sixhat/Pintografo/briefing/assets/pintograph-02.jpeg

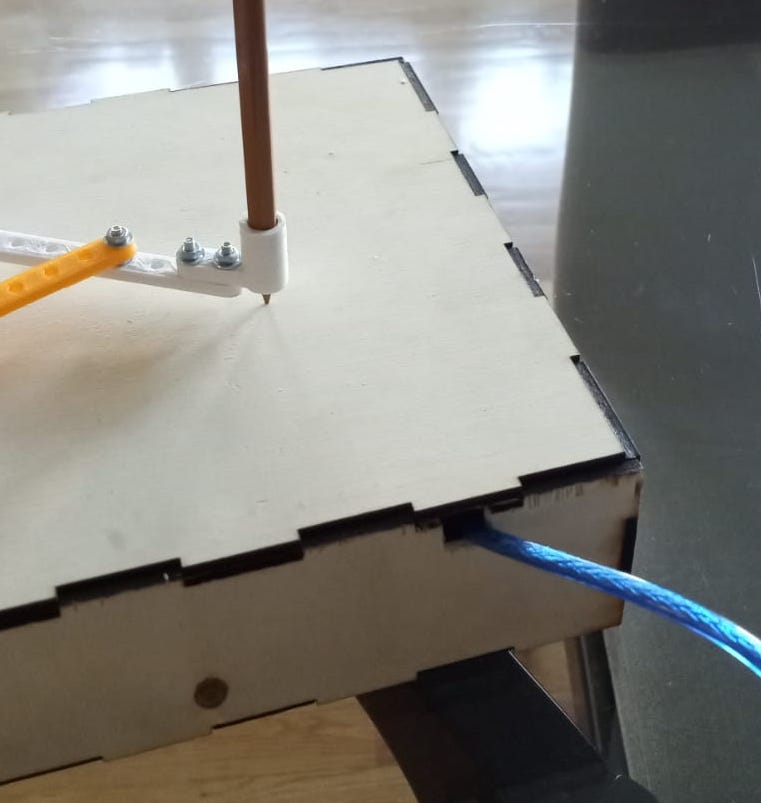
briefing/assets/pintograph-02.jpeg
