sixhat/Pintografo/briefing/assets/ULN2003.jpg

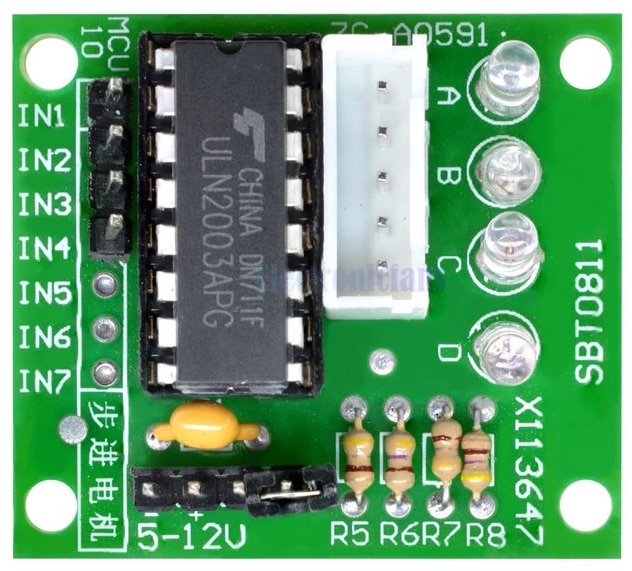
briefing/assets/ULN2003.jpg
