sixhat/Pintografo/media/arms-on-off-button.jpeg

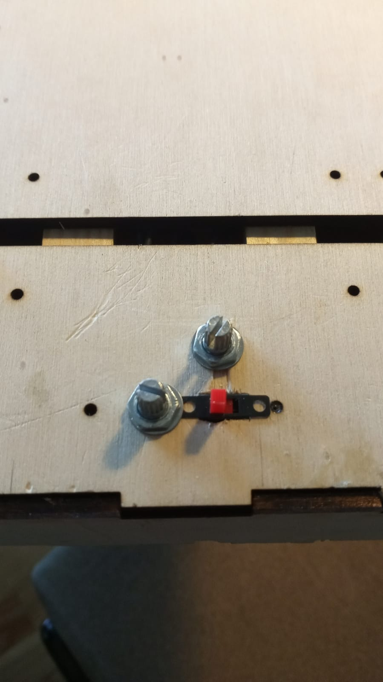
media/arms-on-off-button.jpeg
