sixhat/Pintografo/media/byj-48-steppers.jpeg

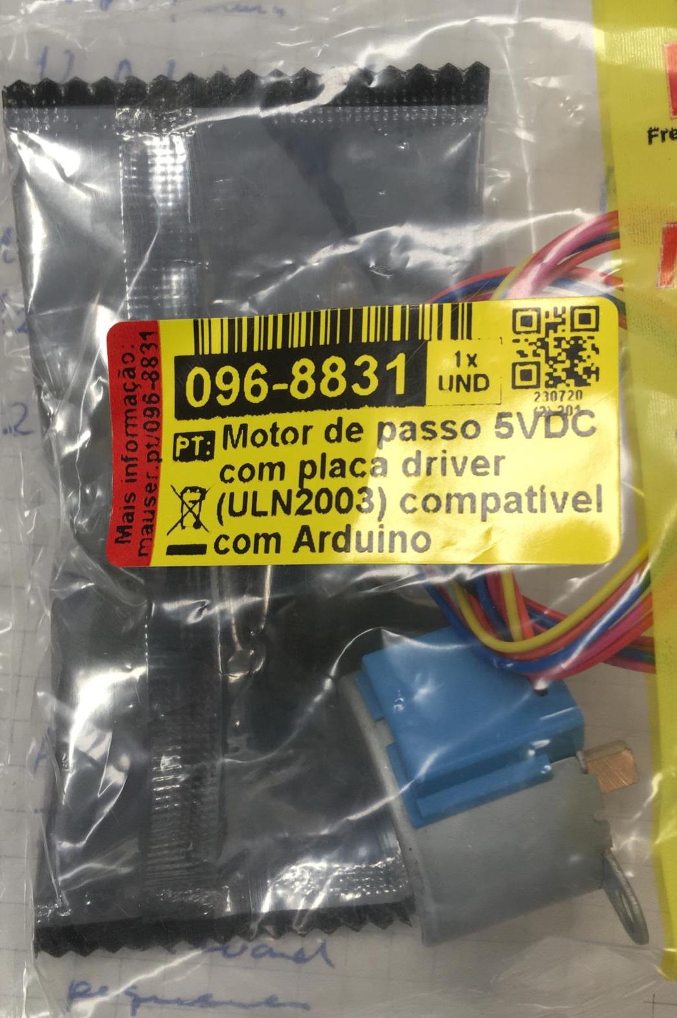
media/byj-48-steppers.jpeg
