sixhat/Pintografo/media/drawing-machine-internals-02.jpeg

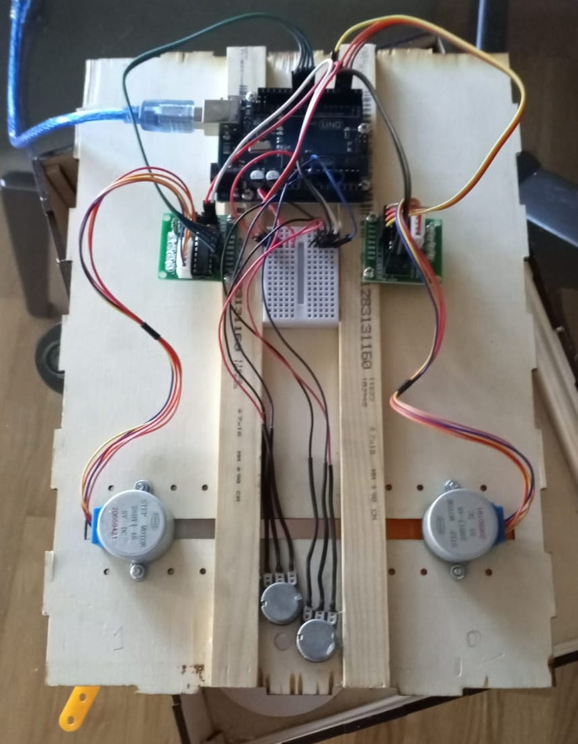
media/drawing-machine-internals-02.jpeg
