sixhat/Pintografo/media/drawing-machine-internals.jpeg

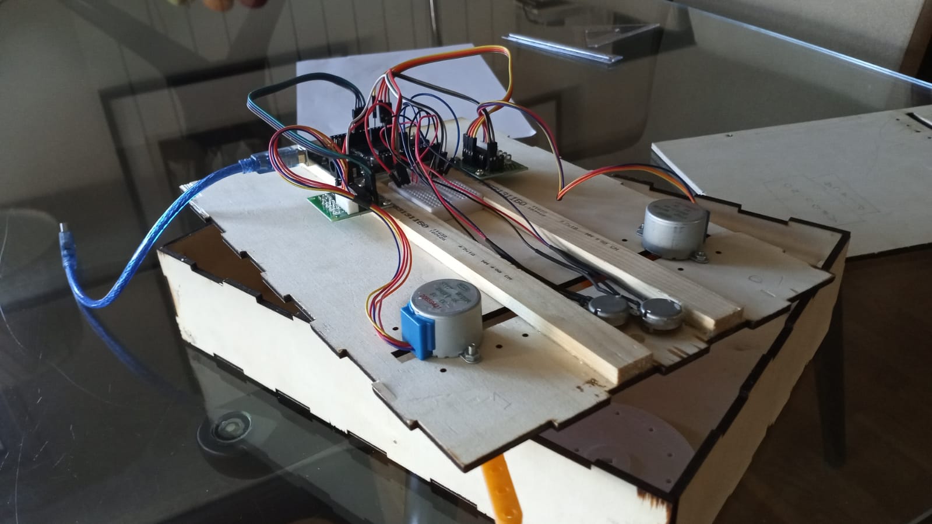
media/drawing-machine-internals.jpeg
