sixhat/Pintografo/media/prototype-working.jpeg

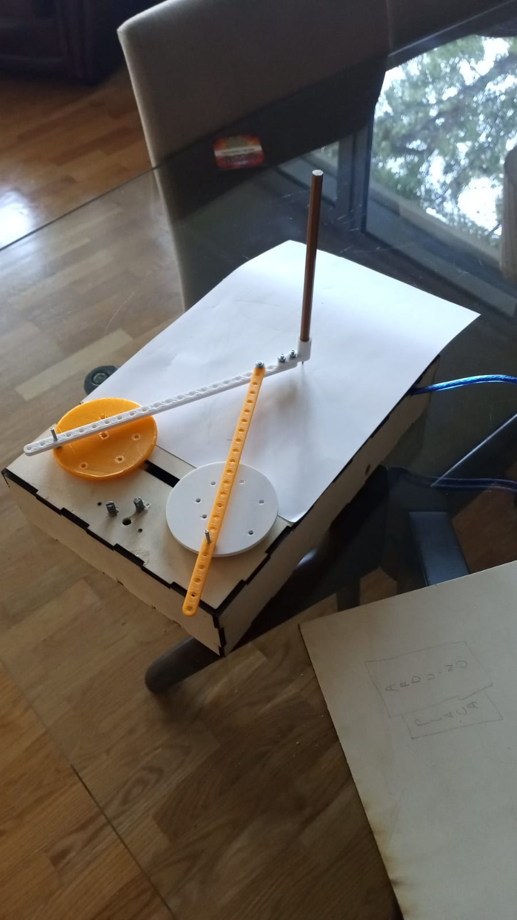
media/prototype-working.jpeg
