sixhat/Pintografo/3Dprinting/stl/pen_holder.stl

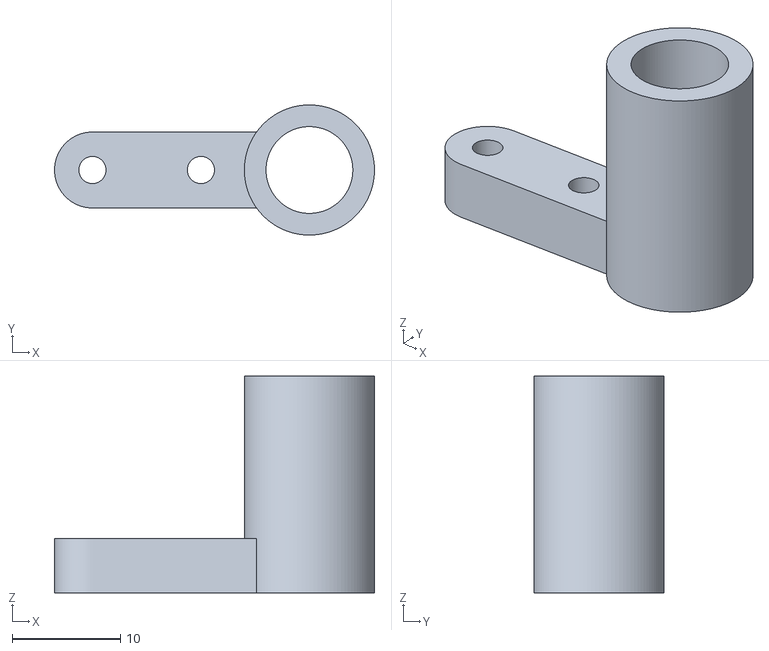
[picture p27: CAD file, 2022-09-26]
3Dprinting/stl/pen_holder.stl
29.5 x 12.0 x 20.0
