sixhat/Pintografo/3Dprinting/stl/spindles_v4.stl

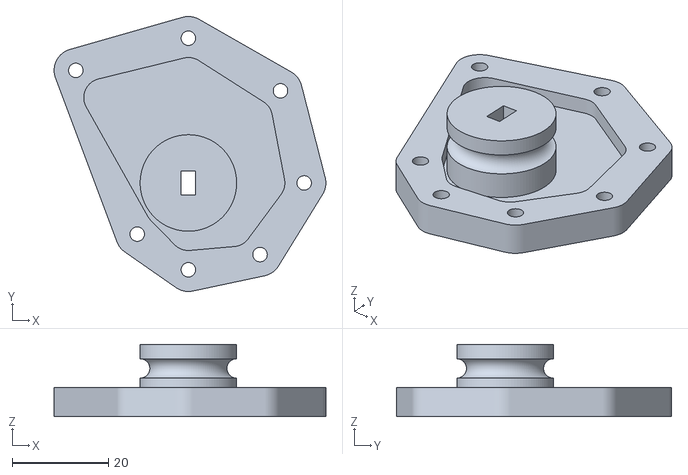
[picture p28: CAD file, 2022-10-15, an earlier design]
3Dprinting/stl/spindles_v4.stl
56.3 x 57.0 x 15.0
