sixhat/Pintografo/media/pen-holder-issue-01.jpeg

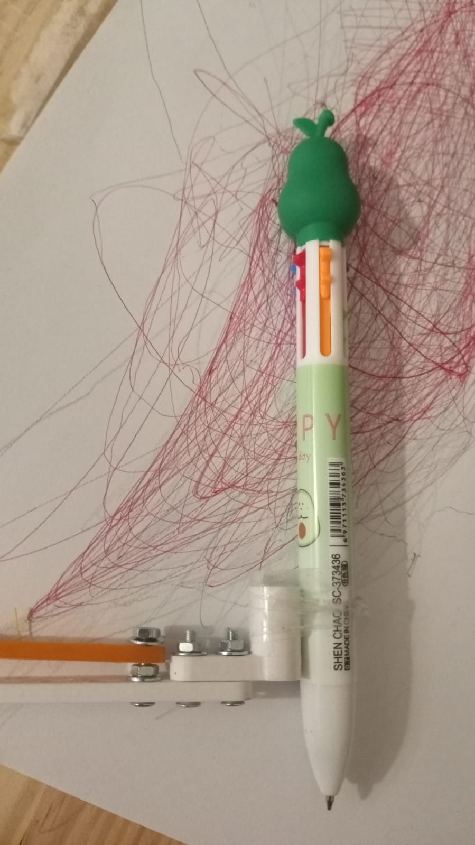
media/pen-holder-issue-01.jpeg
