sixhat/Pintografo/electronics/28BYJ-48_tester/28BYJ-48_tester.ino

#define A 2
#define B 3
#define C 4
#define D 5
#define NUMBER_OF_STEPS_PER_REV 512
#define PAUSA 1

void setup() {
  pinMode(A, OUTPUT);
  pinMode(B, OUTPUT);
  pinMode(C, OUTPUT);
  pinMode(D, OUTPUT);
}

void write(int a, int b, int c, int d) {
  digitalWrite(A, a);
  digitalWrite(B, b);
  digitalWrite(C, c);
  digitalWrite(D, d);
}

void onestep(int dir) {
  if (dir) {
    write(1, 0, 0, 0);
    delay(PAUSA);
    write(1, 1, 0, 0);
    delay(PAUSA);
    write(0, 1, 0, 0);
    delay(PAUSA);
    write(0, 1, 1, 0);
    delay(PAUSA);
    write(0, 0, 1, 0);
    delay(PAUSA);
    write(0, 0, 1, 1);
    delay(PAUSA);
    write(0, 0, 0, 1);
    delay(PAUSA);
    write(1, 0, 0, 1);
    delay(PAUSA);
  } else {
    write(1, 0, 0, 1);
    delay(PAUSA);
    write(0, 0, 0, 1);
    delay(PAUSA);
    write(0, 0, 1, 1);
    delay(PAUSA);
    write(0, 0, 1, 0);
    delay(PAUSA);
    write(0, 1, 1, 0);
    delay(PAUSA);
    write(0, 1, 0, 0);
    delay(PAUSA);
    write(1, 1, 0, 0);
    delay(PAUSA);
    write(1, 0, 0, 0);
    delay(PAUSA);

  }
}


void loop() {
  // put your main code here, to run repeatedly:
  int i;
  i = 0;
  while (i < NUMBER_OF_STEPS_PER_REV) {
    onestep(1);
    i++;
  }
  i = 0;
  while (i < NUMBER_OF_STEPS_PER_REV) {
    onestep(0);
    i++;
  }
}
